silverstee1/ETH2GC-Card-Slot-Adapter/PCB/Kicad Project/BBAMemCardPCB.kicad_sch

## KiCad design PCB/Kicad Project/BBAMemCardPCB.kicad_sch (2024-08-27)

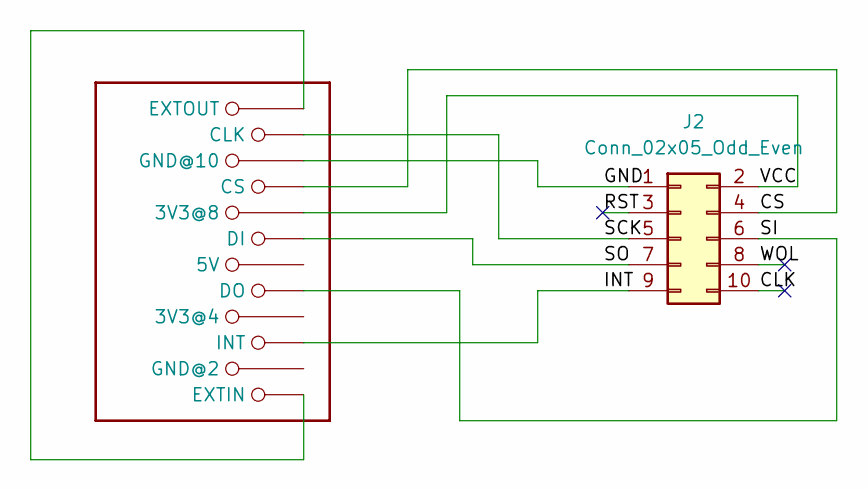
[picture p6: schematic BBAMemCardPCB.kicad_sch]

Parts:
J1: GC_MEMCARD
J2: Conn_02x05_Odd_Even; PinHeader_2x05_P2.54mm_Vertical

Connections:
CLK: J2.10
CS: J1.9 (CS), J2.4
GND: J1.10 (GND@10), J2.1
INT: J1.3 (INT), J2.9
unnamed: J1.1 (EXTIN), J1.12 (EXTOUT)
RST: J2.3
SCK: J1.11 (CLK), J2.5
SI: J1.5 (DO), J2.6
SO: J1.7 (DI), J2.7
VCC: J1.8 (3V3@8), J2.2
WOL: J2.8
